Mknea/projectwork_sch/KiCAD microboard trace-antennalla filet/Älymölkky-F.Cu.pdf

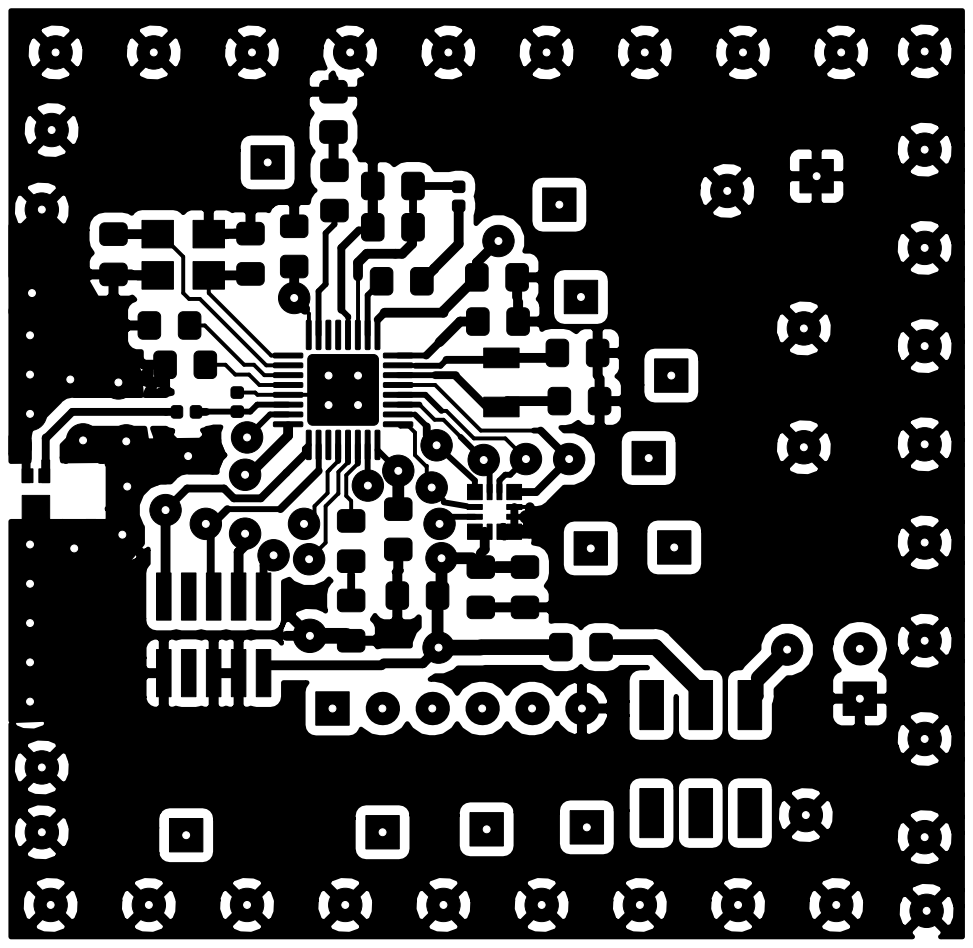
[picture p10: page 1]
